jambamamba/trailcam/hardware/cam.kicad_sch

## KiCad design hardware/cam.kicad_sch (2026-10-05)

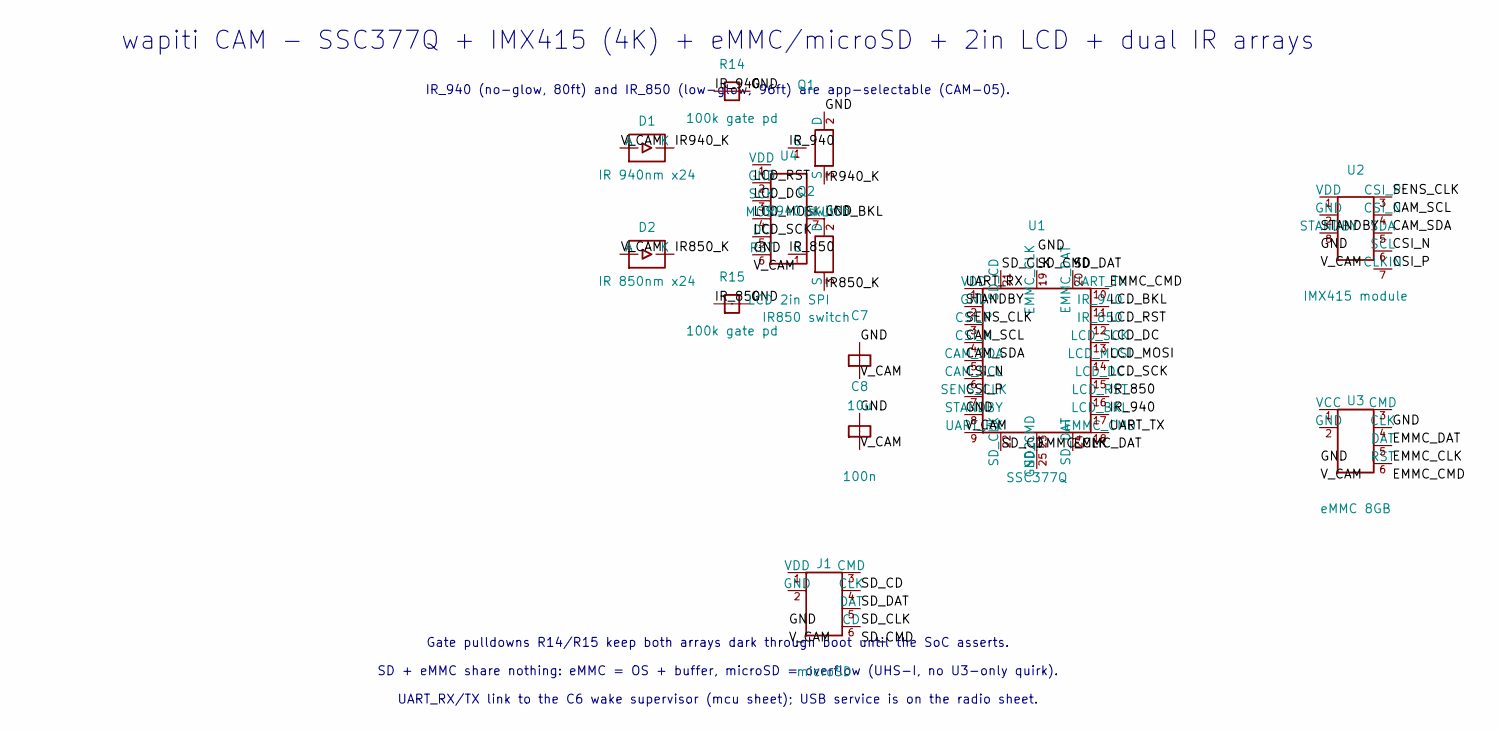
[picture p19: schematic cam.kicad_sch]

Parts:
C7: 10u; C_0603
C8: 100n; C_0603
D1: IR 940nm x24; IR_Array_30x10
D2: IR 850nm x24; IR_Array_30x10
J1: microSD; microSD_Push
Q1: IR940 switch; SOT-23
Q2: IR850 switch; SOT-23
R14, R15: 100k gate pd; R_0603
U1: SSC377Q; SSC377Q_QFN
U2: IMX415 module; IMX415_Module
U3: eMMC 8GB; eMMC_153
U4: LCD 2in SPI; LCD_2in_FPC

Connections:
CAM_SCL: U1.4 (CSI_N), U2.4 (CSI_N)
CAM_SDA: U1.5 (CAM_SDA), U2.5 (SDA)
CSI_N: U1.6 (CAM_SCL), U2.6 (SCL)
CSI_P: U1.7 (SENS_CLK), U2.7 (CLKIN)
EMMC_CLK: U1.23 (SD_CMD), U3.6 (RST)
EMMC_CMD: U1.10 (UART_TX)
EMMC_DAT: U1.24 (SD_DAT), U3.5 (DAT)
GND: C7.1, C8.1, Q1.2 (D), Q2.2 (D), R14.2, R15.2, U1.8 (STANDBY), U3.4 (CLK), U4.6 (RST)
IR850_K: D2.2 (K), Q2.3 (S)
IR940_K: D1.2 (K), Q1.3 (S)
IR_850: Q2.1 (G), R15.1, U1.16 (LCD_RST)
IR_940: Q1.1 (G), R14.1, U1.17 (LCD_BKL)
LCD_BKL: U1.11 (IR_940), U4.7 (BKL)
LCD_DC: U1.13 (LCD_SCK), U4.3 (SCK)
LCD_MOSI: U1.14 (LCD_MOSI), U4.4 (MOSI)
LCD_RST: U1.12 (IR_850), U4.2 (GND)
LCD_SCK: U1.15 (LCD_DC), U4.5 (DC)
SD_CD: J1.4 (CLK), U1.22 (SD_CLK)
SD_CLK: J1.6 (CD), U1.21 (SD_CD)
SD_CMD: U1.19 (EMMC_CLK)
SD_DAT: J1.5 (DAT), U1.20 (EMMC_DAT)
SENS_CLK: U1.3 (CSI_P), U2.3 (CSI_P)
STANDBY: U1.2 (GND), U2.8 (STANDBY)
UART_RX: U1.1 (VDD)
UART_TX: U1.18 (EMMC_CMD)
V_CAM: C7.2, C8.2, D1.1 (A), D2.1 (A), U1.9 (UART_RX)

Notes on the sheet:
wapiti CAM - SSC377Q + IMX415 (4K) + eMMC/microSD + 2in LCD + dual IR arrays
IR_940 (no-glow, 80ft) and IR_850 (low-glow, 96ft) are app-selectable (CAM-05).
Gate pulldowns R14/R15 keep both arrays dark through boot until the SoC asserts.
SD + eMMC share nothing: eMMC = OS + buffer, microSD = overflow (UHS-I, no U3-only quirk).
UART_RX/TX link to the C6 wake supervisor (mcu sheet); USB service is on the radio sheet.
