jambamamba/trailcam/hardware/mcu.kicad_sch

## KiCad design hardware/mcu.kicad_sch (2026-10-05)

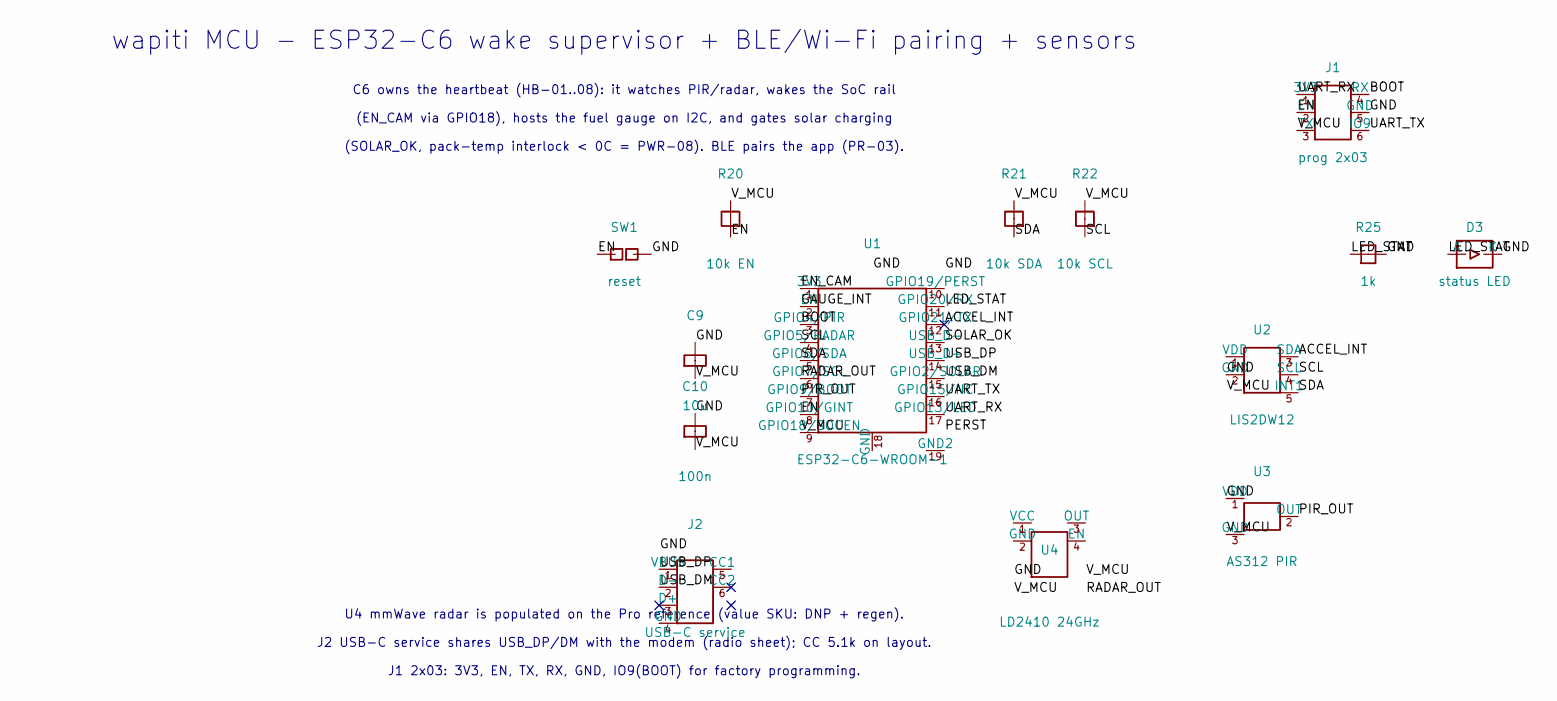
[picture p20: schematic mcu.kicad_sch]

Parts:
C9: 10u; C_0603
C10: 100n; C_0603
D3: status LED; IR_Array_30x10
J1: prog 2x03; PinHeader_2x03_P2.54mm
J2: USB-C service; USB_C_Receptacle_16P
R20: 10k EN; R_0603
R21: 10k SDA; R_0603
R22: 10k SCL; R_0603
R25: 1k; R_0603
SW1: reset; Button_4x4mm
U1: ESP32-C6-WROOM-1
U2: LIS2DW12; LGA-12_2x2mm
U3: AS312 PIR; PIR_Dome
U4: LD2410 24GHz; Radar_LD2410

Connections:
ACCEL_INT: U1.12 (GPIO21/TX), U2.3 (SDA)
BOOT: J1.4 (RX), U1.3 (GPIO4/PIR)
EN: J1.2 (EN), R20.1, SW1.1, U1.8 (GPIO10/GINT)
EN_CAM: U1.1 (3V3)
GAUGE_INT: U1.2 (EN)
GND: C9.1, C10.1, D3.2 (K), J1.5 (GND), R25.2, SW1.2, U2.2 (GND), U3.1 (VDD)
LED_STAT: D3.1 (A), R25.1, U1.11 (GPIO20/RX)
PIR_OUT: U1.7 (GPIO9/BOOT), U3.2 (OUT)
RADAR_OUT: U1.6 (GPIO7/SCL)
SCL: R22.1, U1.4 (GPIO5/RADAR), U2.4 (SCL)
SDA: R21.1, U1.5 (GPIO6/SDA), U2.5 (INT1)
SOLAR_OK: U1.13 (USB_D-)
UART_RX: J1.1 (3V3), U1.17 (GPIO13/LED)
UART_TX: J1.6 (IO9), U1.16 (GPIO15/NC)
USB_DM: J2.2 (D-), U1.15 (GPIO2/SOLAR)
USB_DP: J2.1 (VBUS), U1.14 (USB_D+)
V_MCU: C9.2, C10.2, J1.3 (TX), R20.2, R21.2, R22.2, U1.9 (GPIO18/SOCEN), U3.3 (GND)

Notes on the sheet:
wapiti MCU - ESP32-C6 wake supervisor + BLE/Wi-Fi pairing + sensors
C6 owns the heartbeat (HB-01..08): it watches PIR/radar, wakes the SoC rail
(EN_CAM via GPIO18), hosts the fuel gauge on I2C, and gates solar charging
(SOLAR_OK, pack-temp interlock < 0C = PWR-08). BLE pairs the app (PR-03).
U4 mmWave radar is populated on the Pro reference (value SKU: DNP + regen).
J2 USB-C service shares USB_DP/DM with the modem (radio sheet); CC 5.1k on layout.
J1 2x03: 3V3, EN, TX, RX, GND, IO9(BOOT) for factory programming.
