jambamamba/trailcam/hardware/power.kicad_sch

## KiCad design hardware/power.kicad_sch (2026-10-05)

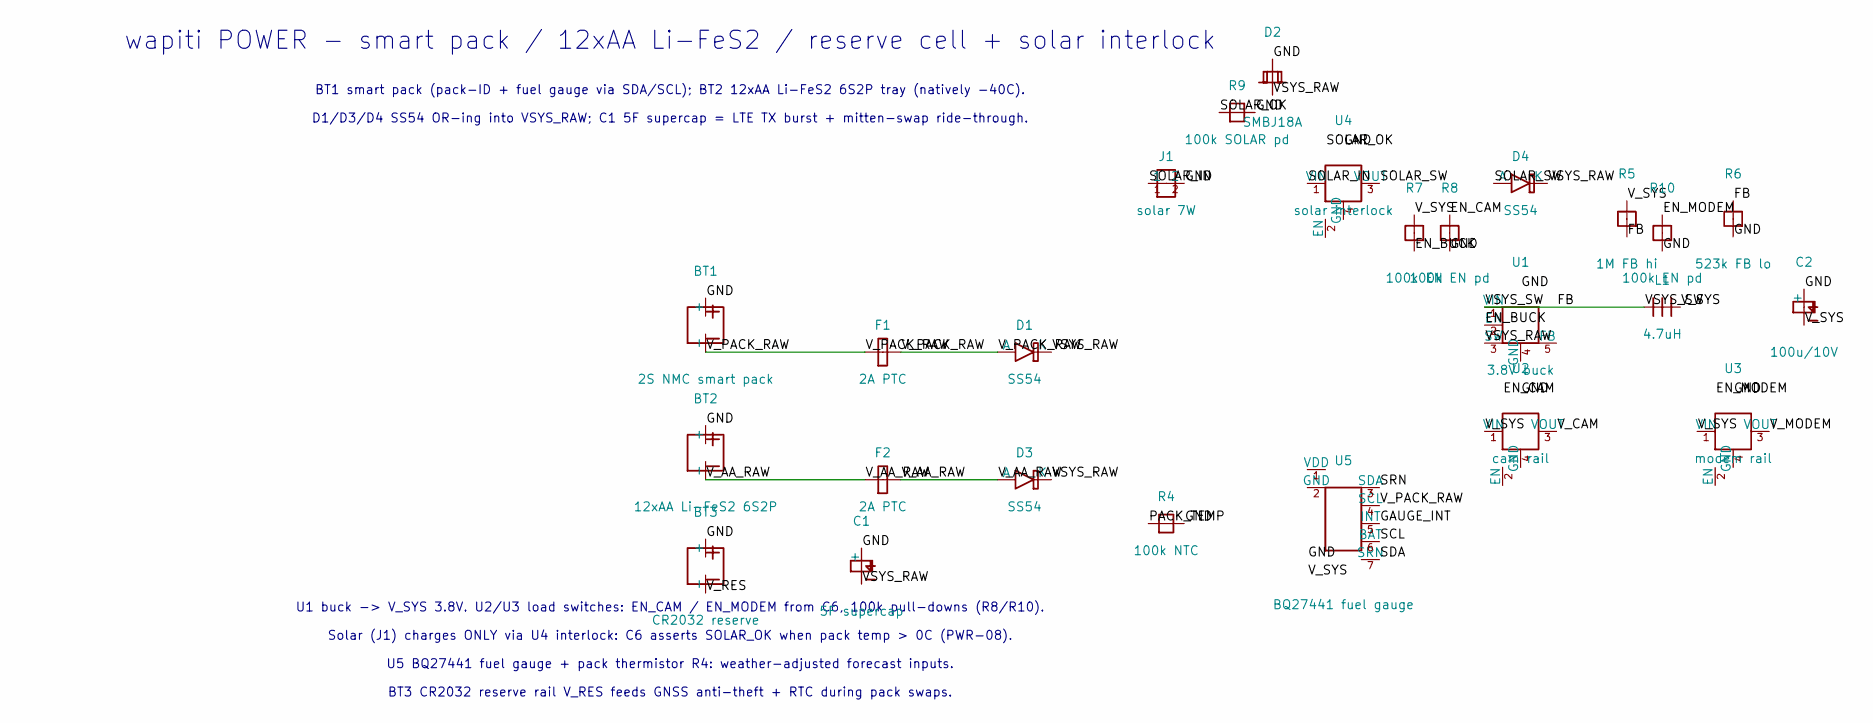
[picture p21: schematic power.kicad_sch]

Parts:
BT1: 2S NMC smart pack; Pack_Conn_5p
BT2: 12xAA Li-FeS2 6S2P; Pack_Conn_5p
BT3: CR2032 reserve; Pack_Conn_5p
C1: 5F supercap; CP_Elec_6.3x7.7
C2: 100u/10V; CP_Elec_6.3x7.7
D1, D3, D4: SS54; Diode_SMA
D2: SMBJ18A; TVS_SOD-323
F1, F2: 2A PTC; Fuse_1206
J1: solar 7W; JST_PH_2p
L1: 4.7uH; L_1210
R4: 100k NTC; R_0603
R5: 1M FB hi; R_0603
R6: 523k FB lo; R_0603
R7: 100k EN; R_0603
R8, R10: 100k EN pd; R_0603
R9: 100k SOLAR pd; R_0603
U1: 3.8V buck; SOIC-8
U2: cam rail; SOT-23-5
U3: modem rail; SOT-23-5
U4: solar interlock; SOT-23-5
U5: BQ27441 fuel gauge; SOT-23-8

Connections:
EN_BUCK: R7.1, U1.2 (EN)
EN_CAM: R8.2
EN_MODEM: R10.2
FB: L1.1, R5.1, R6.2, U1.1 (VIN)
GAUGE_INT: U5.5 (INT)
GND: BT1.1 (+), BT2.1 (+), BT3.1 (+), C1.1 (+), C2.1 (+), D2.1, J1.2, R4.2, R6.1, R8.1, R9.2, R10.1
PACK_TEMP: R4.1
SCL: U5.6 (BAT)
SDA: U5.7 (SRN)
SOLAR_IN: J1.1, U4.1 (VIN)
SOLAR_OK: R9.1
SOLAR_SW: D4.1 (A), U4.3 (VOUT)
SRN: U5.3 (SDA)
VSYS_RAW: C1.2, D1.2 (K), D2.2, D3.2 (K), D4.2 (K), U1.3 (SW)
V_AA_RAW: BT2.2 (-), D3.1 (A), F2.1, F2.2
V_CAM: U2.3 (VOUT)
V_MODEM: U3.3 (VOUT)
V_PACK_RAW: BT1.2 (-), D1.1 (A), F1.1, F1.2, U5.4 (SCL)
V_RES: BT3.2 (-)
V_SYS: C2.2, L1.2, R5.2, R7.2, U2.1 (VIN), U3.1 (VIN)

Notes on the sheet:
wapiti POWER - smart pack / 12xAA Li-FeS2 / reserve cell + solar interlock
BT1 smart pack (pack-ID + fuel gauge via SDA/SCL); BT2 12xAA Li-FeS2 6S2P tray (natively -40C).
D1/D3/D4 SS54 OR-ing into VSYS_RAW; C1 5F supercap = LTE TX burst + mitten-swap ride-through.
U1 buck -> V_SYS 3.8V. U2/U3 load switches: EN_CAM / EN_MODEM from C6, 100k pull-downs (R8/R10).
Solar (J1) charges ONLY via U4 interlock: C6 asserts SOLAR_OK when pack temp > 0C (PWR-08).
U5 BQ27441 fuel gauge + pack thermistor R4: weather-adjusted forecast inputs.
BT3 CR2032 reserve rail V_RES feeds GNSS anti-theft + RTC during pack swaps.
