jambamamba/trailcam/hardware/radio.kicad_sch

## KiCad design hardware/radio.kicad_sch (2026-10-05)

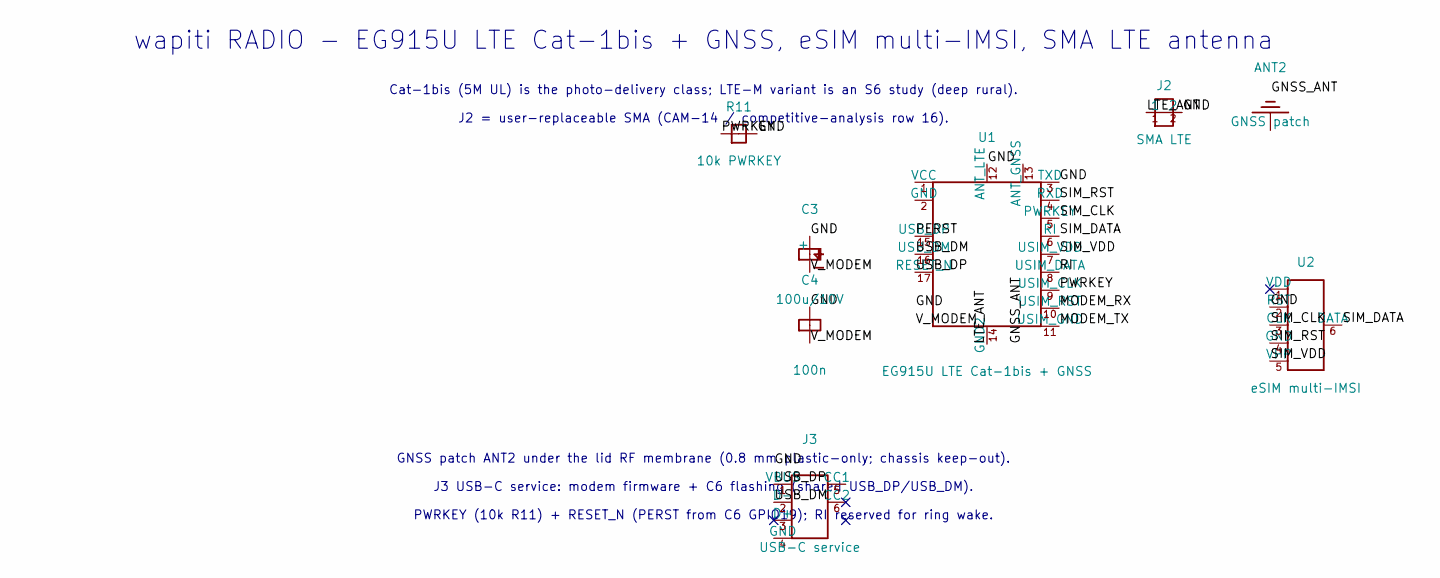
[picture p22: schematic radio.kicad_sch]

Parts:
ANT2: GNSS patch; Antenna_UMWiSE_1.6mm
C3: 100u/10V; CP_Elec_6.3x7.7
C4: 100n; C_0603
J2: SMA LTE; JST_PH_2p
J3: USB-C service; USB_C_Receptacle_16P
R11: 10k PWRKEY; R_0603
U1: EG915U LTE Cat-1bis + GNSS; EG915U
U2: eSIM multi-IMSI; NanoSIM_Push

Connections:
GND: C3.1 (+), C4.1, J2.2, R11.2, U1.3 (TXD), U1.12 (ANT_LTE), U2.2 (RST)
LTE_ANT: J2.1, U1.14 (GND2)
MODEM_RX: U1.10 (USIM_RST)
MODEM_TX: U1.11 (USIM_GND)
PERST: U1.15 (USB_DP)
PWRKEY: R11.1, U1.9 (USIM_CLK)
RI: U1.8 (USIM_DATA)
SIM_CLK: U1.5 (PWRKEY), U2.3 (CLK)
SIM_DATA: U1.6 (RI), U2.6 (DATA)
SIM_RST: U1.4 (RXD), U2.4 (GND)
SIM_VDD: U1.7 (USIM_VDD), U2.5 (VPP)
USB_DM: J3.2 (D-), U1.16 (USB_DM)
USB_DP: J3.1 (VBUS), U1.17 (RESET_N)
V_MODEM: C3.2, C4.2

Notes on the sheet:
wapiti RADIO - EG915U LTE Cat-1bis + GNSS, eSIM multi-IMSI, SMA LTE antenna
Cat-1bis (5M UL) is the photo-delivery class; LTE-M variant is an S6 study (deep rural).
J2 = user-replaceable SMA (CAM-14 / competitive-analysis row 16).
GNSS patch ANT2 under the lid RF membrane (0.8 mm plastic-only; chassis keep-out).
J3 USB-C service: modem firmware + C6 flashing (shared USB_DP/USB_DM).
PWRKEY (10k R11) + RESET_N (PERST from C6 GPIO19); RI reserved for ring wake.
